hiureanderson/FTIR-Spectro/Docs/Quotes/DOC041415-001.pdf

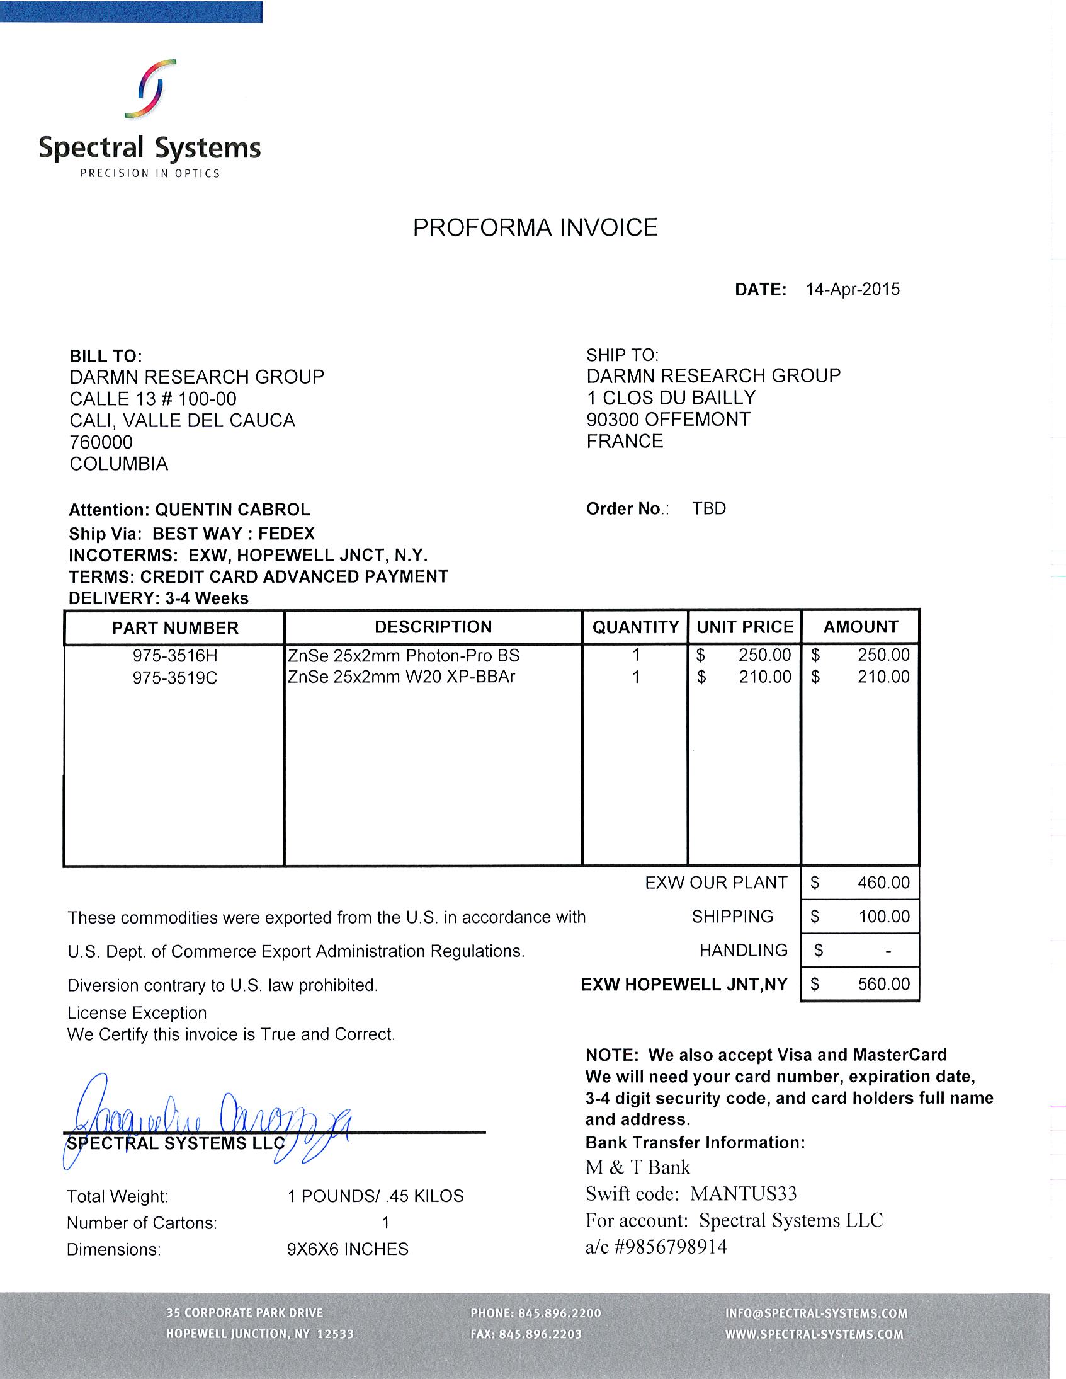
[picture p6: page 1]
