hiureanderson/FTIR-Spectro/pictures/IMG_20150918_115104.jpg

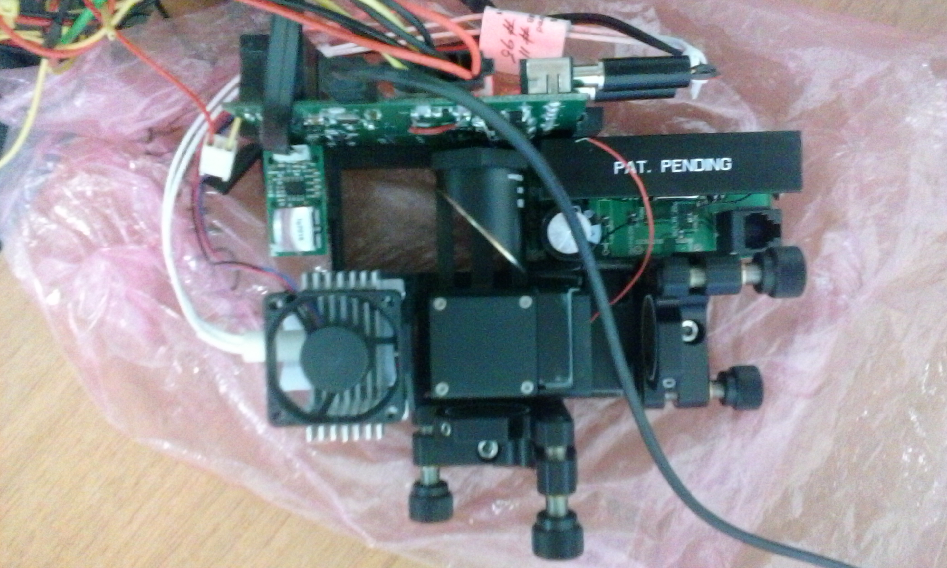
pictures/IMG_20150918_115104.jpg
