hiureanderson/FTIR-Spectro/pictures/IMG_20150918_115118.jpg

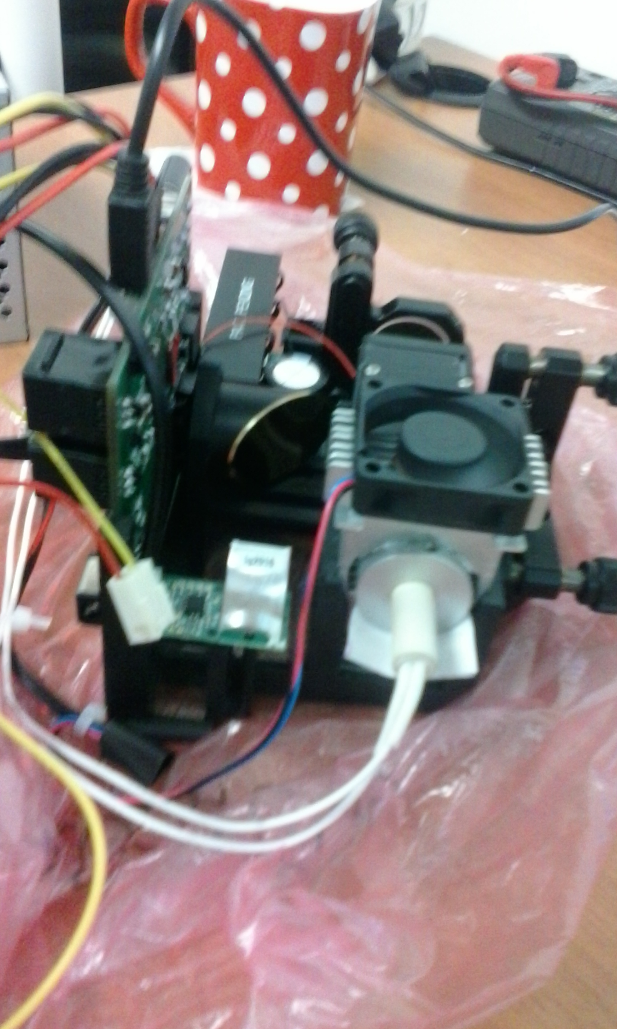
pictures/IMG_20150918_115118.jpg
