hiureanderson/FTIR-Spectro/pictures/photo_2015-09-12_13-54-08.jpg

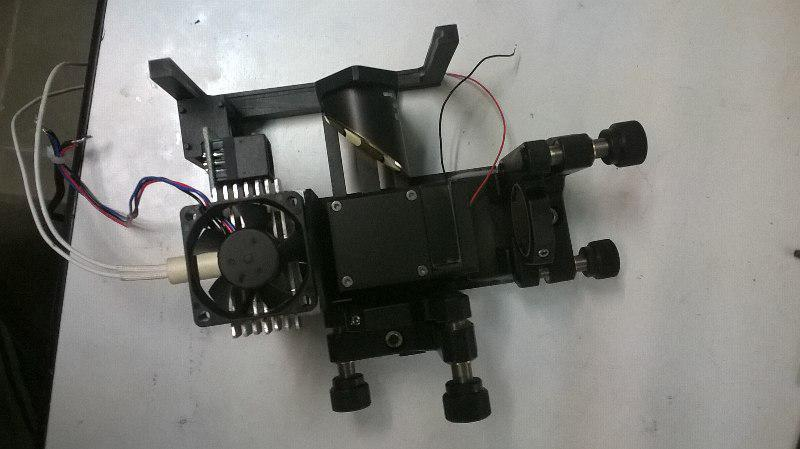
pictures/photo_2015-09-12_13-54-08.jpg
