hiureanderson/FTIR-Spectro/pictures/photo_2015-09-12_13-55-24.jpg

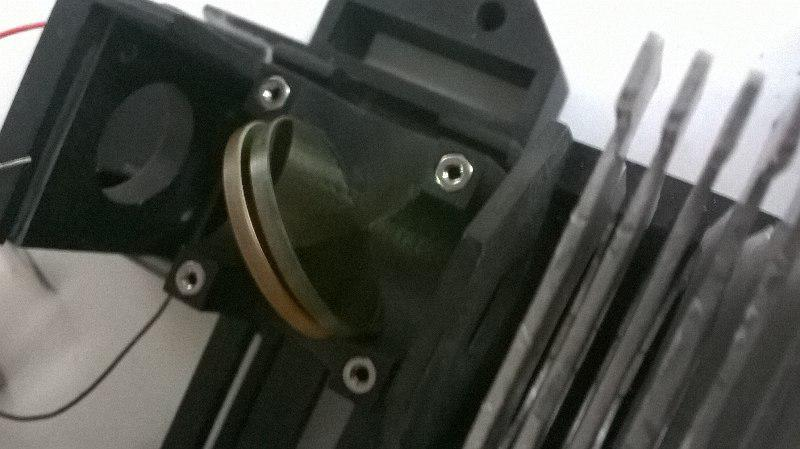
pictures/photo_2015-09-12_13-55-24.jpg
