hiureanderson/FTIR-Spectro/pictures/photo_2015-09-12_13-57-03.jpg

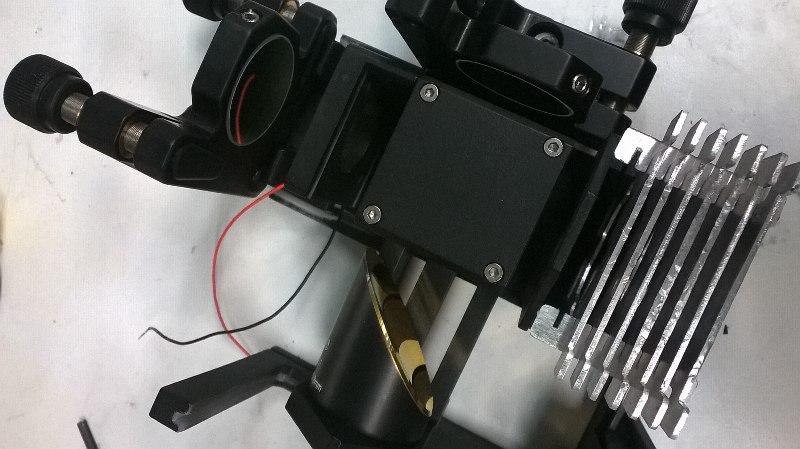
pictures/photo_2015-09-12_13-57-03.jpg
