hiureanderson/FTIR-Spectro/CAD/Splitter.fcstd

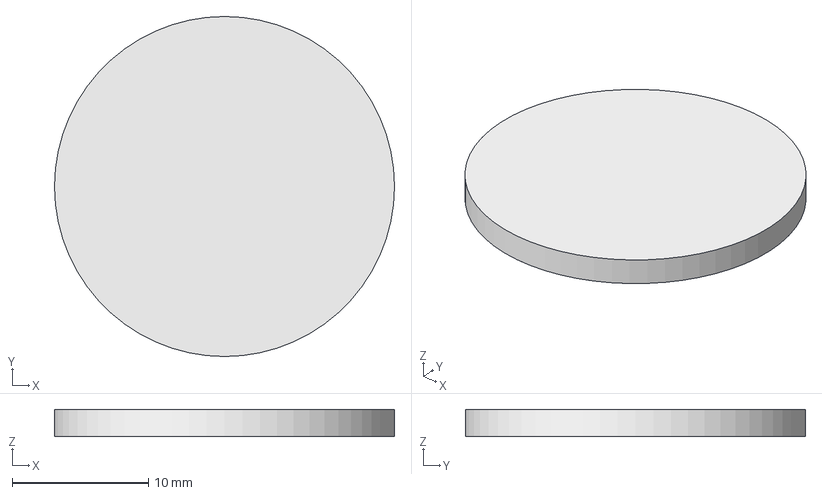
[picture p27: CAD file, 2015-07-17]
CAD/Splitter.fcstd
25.0 x 25.0 x 2.00 mm
