hiureanderson/FTIR-Spectro/CAD/Mirror.fcstd

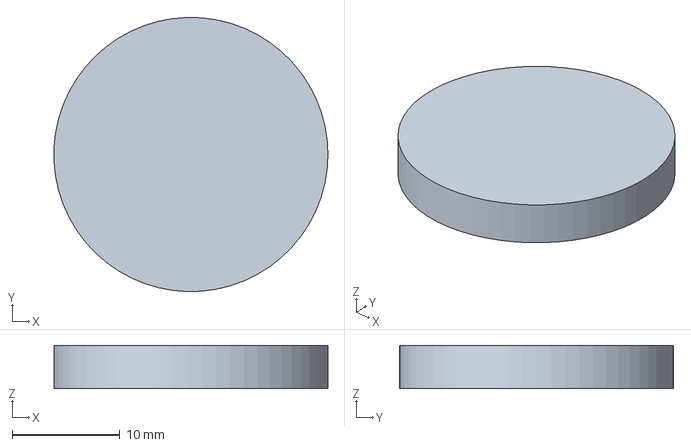
[picture p28: CAD file, 2015-07-17]
CAD/Mirror.fcstd
25.4 x 25.4 x 4.00 mm
