hiureanderson/FTIR-Spectro/CAD/FTIR.fcstd

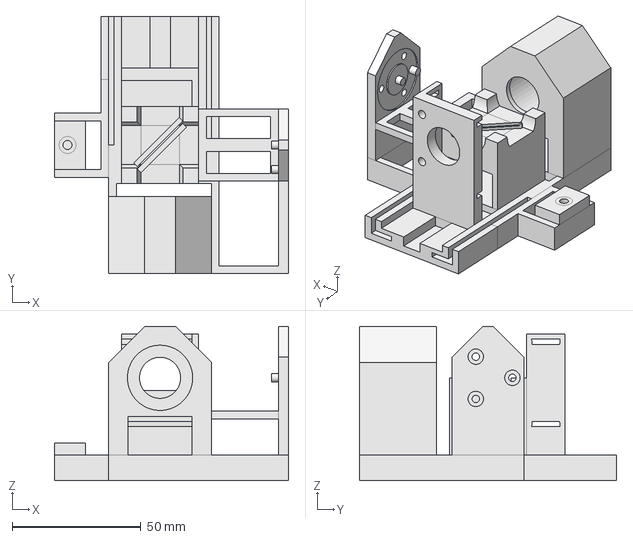
[picture p29: CAD file, 2015-07-16]
CAD/FTIR.fcstd
91.1 x 100.0 x 60.0 mm
