hiureanderson/FTIR-Spectro/CAD/STL/MPD129-M01-Step.step

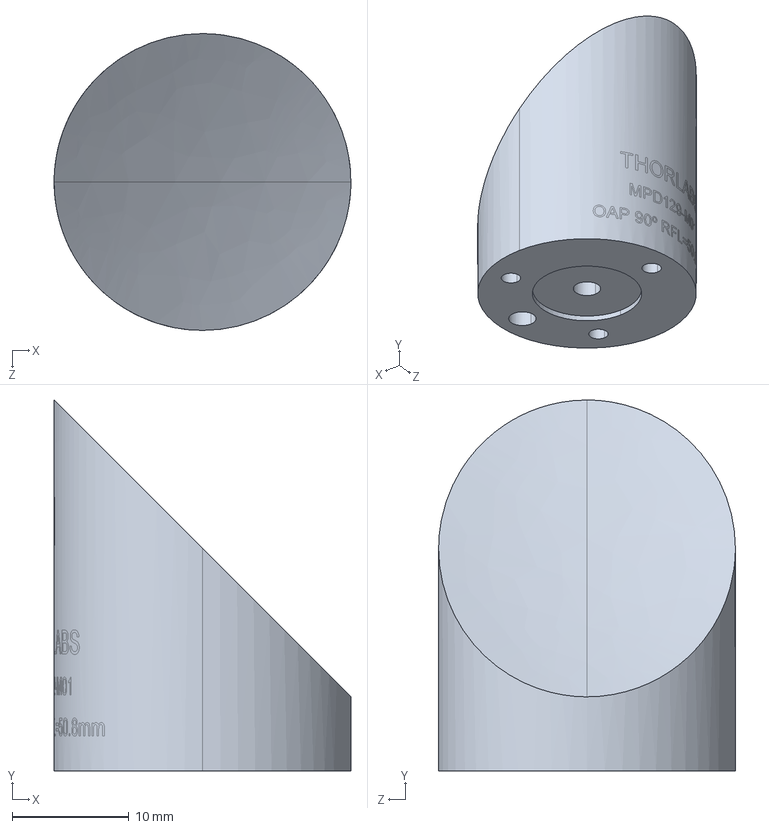
[picture p30: CAD file, 2015-07-17]
CAD/STL/MPD129-M01-Step.step
25.4 x 31.7 x 25.4 mm
