hiureanderson/FTIR-Spectro/CAD/STL/KM100-Step.step

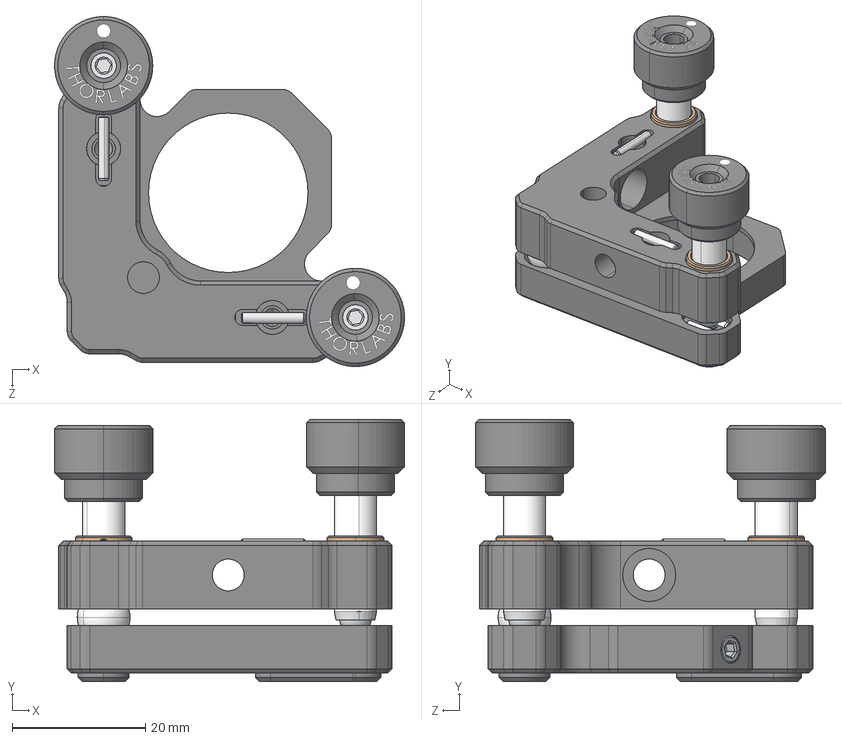
[picture p31: CAD file, 2015-07-17]
CAD/STL/KM100-Step.step
52.4 x 39.3 x 52.4 mm
